nullvalue0/Cromemco-Cyclops-88-CCC-Reproduction/Original Images/1_633fe38ef0db4985cfbc20734cecd3d22.jpg

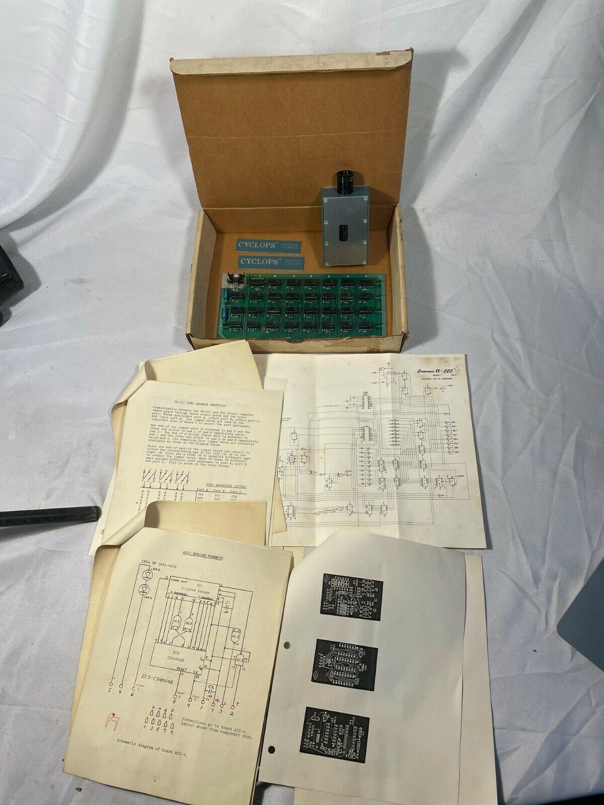
Original Images/1_633fe38ef0db4985cfbc20734cecd3d22.jpg
