nullvalue0/Cromemco-Cyclops-88-CCC-Reproduction/Original Images/1_4693db02673373e849629bbae9dc3f28.jpg

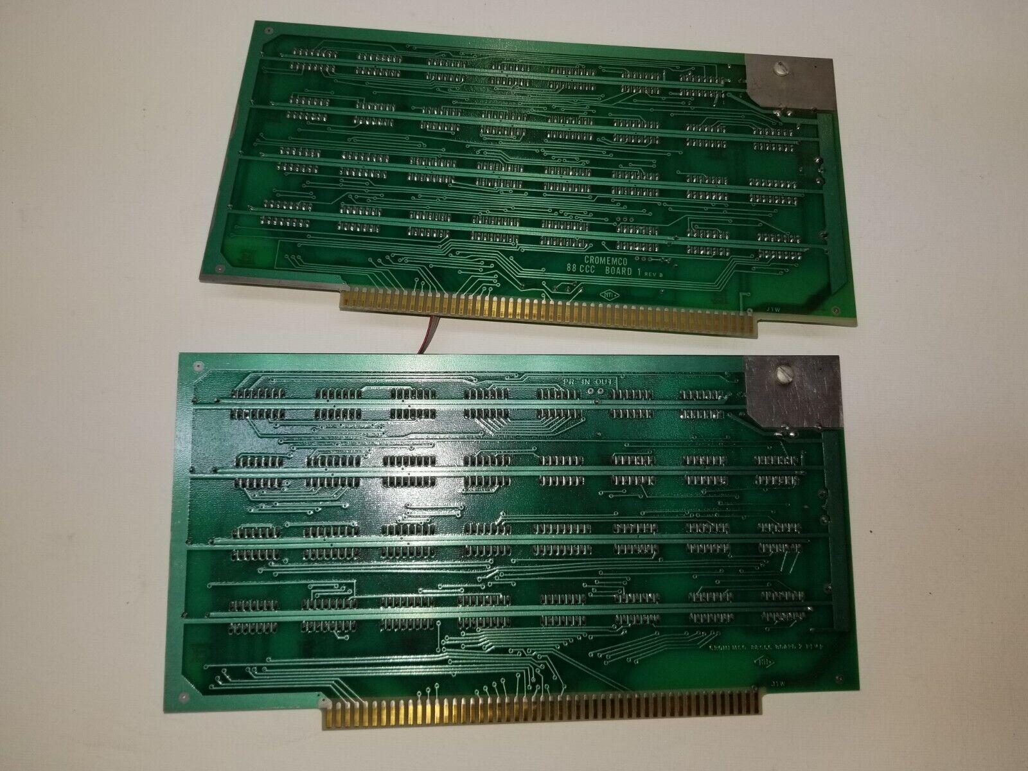
Original Images/1_4693db02673373e849629bbae9dc3f28.jpg
