nullvalue0/Cromemco-Cyclops-88-CCC-Reproduction/Original Images/1_7216d526ae64bc634e5076556dfacafa.jpg

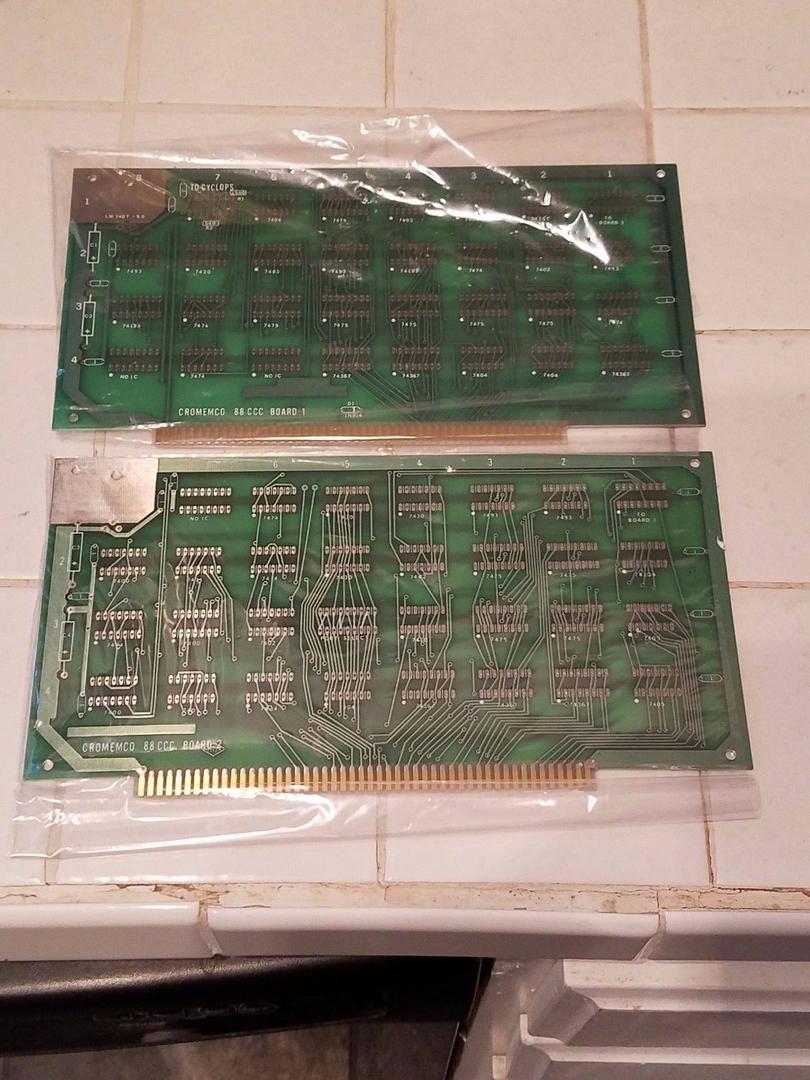
Original Images/1_7216d526ae64bc634e5076556dfacafa.jpg
