nullvalue0/Cromemco-Cyclops-88-CCC-Reproduction/Original Images/88 CCC Board 1 back.JPG

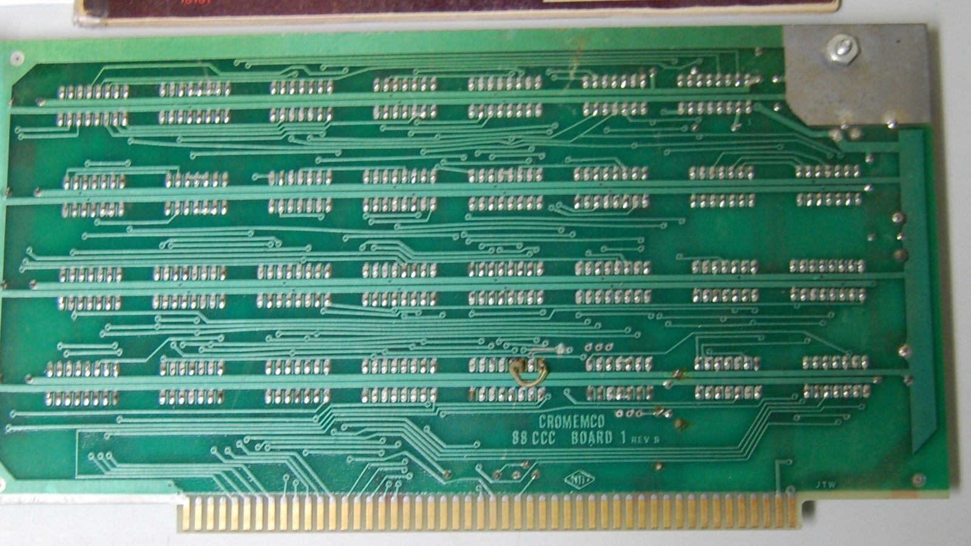
Original Images/88 CCC Board 1 back.JPG
