nullvalue0/Cromemco-Cyclops-88-CCC-Reproduction/Original Images/88 CCC Board 2.JPG

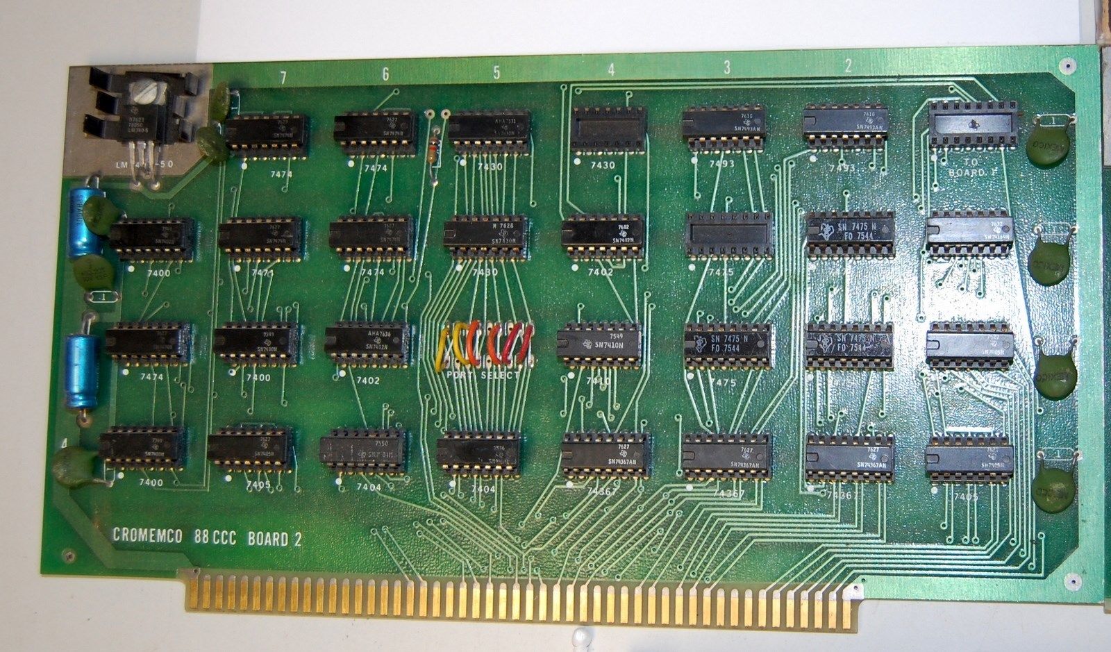
Original Images/88 CCC Board 2.JPG
