nullvalue0/Cromemco-Cyclops-88-CCC-Reproduction/Original Images/Cyclops board set.JPG

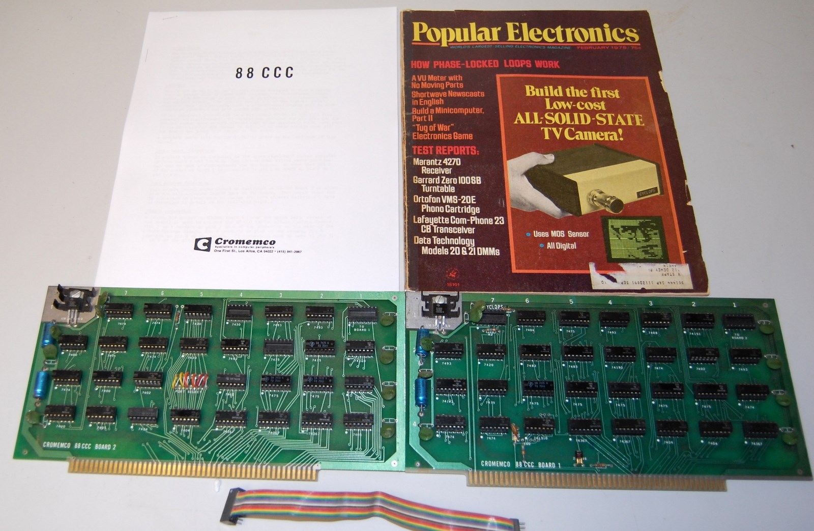
Original Images/Cyclops board set.JPG
